MathiasKoch/uwb_localization/Inc/hal.h

/**
  ******************************************************************************
  * @file    hal.h
  * @brief   HAL configuration file.  
  ******************************************************************************
  * @attention
  *
  * <h2><center>&copy; COPYRIGHT(c) 2016 STMicroelectronics</center></h2>
  *
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
  ******************************************************************************
  */ 

/* Define to prevent recursive inclusion -------------------------------------*/
#ifndef __HAL_H
#define __HAL_H

#ifdef __cplusplus
 extern "C" {
#endif

#include "error.h"

#if defined  (STM32F302xC) 
  #include "stm32f3xx_hal.h"
  #include "stm32f3xx.h"

  /* Decawave pin defines */
  #define DECA_SPI_INSTANCE (SPI1)

  #define DECA_CS_PORT (GPIOA)
  #define DECA_CS_PIN (GPIO_PIN_4)

  #define DECA_IRQ_PORT (GPIOB)
  #define DECA_IRQ_PIN (GPIO_PIN_0)
  #define DECA_IRQ_EXTI (EXTI0_IRQn)

  #define DECA_RESET_PORT (GPIOA)
  #define DECA_RESET_PIN (GPIO_PIN_8)

  /* Userbutton pin defines */
  #define USER_BUTTON_PORT (GPIOA)
  #define USER_BUTTON_PIN (GPIO_PIN_1)
  #define USER_BUTTON_EXTI (EXTI1_IRQn)

  /* Enable client SPI (SPI2) */
  #define CLIENT_SPI_INSTANCE (SPI2)

  /* IMU/PRESSURE pin defines */                                                      //------------------ These might still be wrong!
  #define IMU_I2C_INSTANCE (I2C1)

  #define IMU_IRQ_PORT ()
  #define IMU_IRQ_PIN ()
  #define IMU_IRQ_EXTI ()

  /* LED pin defines */                                                      //------------------ These might still be wrong!
  #define LED_1_PORT (GPIOC)
  #define LED_1_PIN (GPIO_PIN_13)
  #define LED_2_PORT (GPIOC)
  #define LED_2_PIN (GPIO_PIN_14)

  /*
  * Everything below here is processor specific defines, and should as such
  * NOT need to be edited! They are specific for the individual processor type,
  * and not implementation specific.
  */

  /* USB pin defines */
  #define USB_PORT (GPIOA)
  #define USBDM_PIN (GPIO_PIN_11)
  #define USBDP_PIN (GPIO_PIN_12)
  #define USB_AF (GPIO_AF14_USB)
  #define USB_EXTI (USB_LP_CAN_RX0_IRQn)

  /* SPI pin defines */
  #define SPI1_PORT (GPIOA)
  #define SPI1_SCK_PIN (GPIO_PIN_5)
  #define SPI1_MISO_PIN (GPIO_PIN_6)
  #define SPI1_MOSI_PIN (GPIO_PIN_7)
  #define SPI1_AF (GPIO_AF5_SPI1)

  #define SPI2_PORT (GPIOB)
  #define SPI2_SCK_PIN (GPIO_PIN_13)
  #define SPI2_MISO_PIN (GPIO_PIN_14)
  #define SPI2_MOSI_PIN (GPIO_PIN_15)
  #define SPI2_AF (GPIO_AF5_SPI2)

  #define DMA1_CHAN2_EXTI (DMA1_Channel2_IRQn)
  #define DMA1_CHAN3_EXTI (DMA1_Channel3_IRQn)

  /* I2C pin defines */
  #define I2C1_PORT (GPIOB)
  #define I2C1_SCL_PIN (GPIO_PIN_6)
  #define I2C1_SDA_PIN (GPIO_PIN_7)
  #define I2C1_AF (GPIO_AF4_I2C1)

  /*
  * The STM32 factory-programmed UUID memory.
  * Three values of 32 bits each starting at this address
  * Use like this: STM32_UUID[0], STM32_UUID[1], STM32_UUID[2]
  */
  #define STM32_UUID ((uint32_t *)0x1FFFF7AC)

  /* DFU Bootloader defines */                                                      //------------------ These might still be wrong!
  #define SYSMEM_RESET_VECTOR (0x1fffC804)
  #define BOOTLOADER_STACK_POINTER (0x20002250)



#elif defined (STM32F10X_MD)
  #include "stm32f1xx_hal.h"
  #include "stm32f1xx.h"


















#elif defined (STM32F072xB)
  #include "stm32f0xx_hal.h"
  #include "stm32f0xx.h"

  /* Decawave pin defines */
  #define DECA_SPI_INSTANCE (SPI1)

  #define DECA_CS_PORT (GPIOA)
  #define DECA_CS_PIN (GPIO_PIN_4)

  #define DECA_IRQ_PORT (GPIOB)
  #define DECA_IRQ_PIN (GPIO_PIN_0)
  #define DECA_IRQ_EXTI (EXTI0_1_IRQn)

  #define DECA_RESET_PORT (GPIOB)
  #define DECA_RESET_PIN (GPIO_PIN_12)

  /* Userbutton pin defines */
  #define USER_BUTTON_PORT (GPIOA)
  #define USER_BUTTON_PIN (GPIO_PIN_1)
  #define USER_BUTTON_EXTI (EXTI0_1_IRQn)

  /* IMU/PRESSURE pin defines */                                                      //------------------ These might still be wrong!
  #define IMU_I2C_INSTANCE (I2C1)

  #define IMU_IRQ_PORT ()
  #define IMU_IRQ_PIN ()
  #define IMU_IRQ_EXTI ()

  /* LED pin defines */                                                      //------------------ These might still be wrong!
  #define LED_1_PORT (GPIOC)
  #define LED_1_PIN (GPIO_PIN_13)
  #define LED_2_PORT (GPIOC)
  #define LED_2_PIN (GPIO_PIN_14)
  #define LED_CHARGING_PORT (GPIOC)
  #define LED_CHARGING_PIN (GPIO_PIN_14)

  /*
  * Everything below here is processor specific defines, and should as such
  * NOT need to be edited! They are specific for the individual processor type,
  * and not implementation specific.
  */

  /* USB pin defines */
  #define USB_AF (GPIO_AF14_USB)
  #define USB_EXTI (USB_IRQn)

  /* SPI pin defines */
  #define SPI1_PORT (GPIOA)
  #define SPI1_SCK_PIN (GPIO_PIN_5)
  #define SPI1_MISO_PIN (GPIO_PIN_6)
  #define SPI1_MOSI_PIN (GPIO_PIN_7)
  #define SPI1_AF (GPIO_AF0_SPI1)

  #define DMA1_CHAN2_3_EXTI (DMA1_Channel2_3_IRQn)

  /* I2C pin defines */
  #define I2C1_PORT (GPIOB)
  #define I2C1_SCL_PIN (GPIO_PIN_6)
  #define I2C1_SDA_PIN (GPIO_PIN_7)
  #define I2C1_AF (GPIO_AF1_I2C1)
  
  /*
  * The STM32 factory-programmed UUID memory.
  * Three values of 32 bits each starting at this address
  * Use like this: STM32_UUID[0], STM32_UUID[1], STM32_UUID[2]
  */
  #define STM32_UUID ((uint32_t *)0x1FFFF7AC)

  /* DFU Bootloader defines */
  #define SYSMEM_RESET_VECTOR (0x1fffC804)
  #define BOOTLOADER_STACK_POINTER (0x20002250)



#else
  #error "Please first define the target STM32Fxxx device used in your application (in a Makefile define)"
#endif

    
#ifdef __cplusplus
}
#endif

#endif /* __HAL_H */

/************************ (C) COPYRIGHT STMicroelectronics *****END OF FILE****/
