MathiasKoch/uwb_localization/Inc/packet.h

/*
 $License:
    Copyright (C) 2010 InvenSense Corporation, All Rights Reserved.
 $
 */
/*******************************************************************************
 * $Id: $
 *******************************************************************************/

/**
 *  @defgroup STM32L STM32L System Layer
 *  @brief  STM32L System Layer APIs.
 *          To interface with any platform, eMPL needs access to various
 *          system layer functions.
 *
 *  @{
 *      @file   packet.h
 *      @brief  Defines needed for sending data/debug packets via USB.
 */

#ifndef __PACKET_H__
#define __PACKET_H__

#ifdef __cplusplus
extern "C" {
#endif


typedef enum {
    PACKET_DATA_ACCEL = 0,
    PACKET_DATA_GYRO,
    PACKET_DATA_COMPASS,
    PACKET_DATA_QUAT,
    PACKET_DATA_EULER,
    PACKET_DATA_ROT,
    PACKET_DATA_HEADING,
    PACKET_DATA_LINEAR_ACCEL,
    NUM_DATA_PACKETS
} eMPL_packet_e;

/**
 *  @brief      Send a quaternion packet via UART.
 *  The host is expected to use the data in this packet to graphically
 *  represent the device orientation. To send quaternion in the same manner
 *  as any other data packet, use eMPL_send_data.
 *  @param[in]  quat    Quaternion data.
 */
void eMPL_send_quat(long *quat);

/**
 *  @brief      Send a DWM packet via UART.
 *  The host is expected to use the data in this packet to graphically
 *  represent the device positions. 
 *  @param[in]  anchorState     Anchor state data.
 *  @param[in]  noAnchors       No of anchors represented in anchorState.
 *  @param[in]  tagState        Tag state data.
 */
void eMPL_send_dwm(float **anchorState, int noAnchors, float *tagState);

/**
 *  @brief      Send a data packet via UART
 *  @param[in]  type    Contents of packet (PACKET_DATA_ACCEL, etc).
 *  @param[in]  data    Data (length dependent on contents).
 */
void eMPL_send_data(unsigned char type, long *data);


#ifdef __cplusplus
}
#endif

#endif /* __PACKET_H__ */

/**
 * @}
 */
