MathiasKoch/uwb_localization/usb_test.ioc

Mcu.UserName=STM32F302CCTx
PA1.Signal=GPIO_Input
PA11.Signal=USB_DM
PA12.Signal=USB_DP
PA13.Signal=SYS_JTMS-SWDIO
PA14.Signal=SYS_JTCK-SWCLK
PA3.Signal=GPXTI3
PA4.Signal=GPIO_Output
PA5.Signal=SPI1_SCK
PA6.Signal=SPI1_MISO
PA7.Signal=SPI1_MOSI
PA8.Signal=GPIO_Input
PA9.Signal=GPXTI9
PB0.Signal=GPXTI0
PB1.Signal=GPIO_Input
PB12.Signal=GPIO_Input
PB13.Signal=SPI2_SCK
PB14.Signal=SPI2_MISO
PB15.Signal=SPI2_MOSI
PB4.Signal=GPXTI4
PB6.Signal=I2C1_SCL
PB7.Signal=I2C1_SDA
PC13.Signal=GPIO_Output
PC14-OSC32_IN.Signal=GPIO_Output
PF0-OSC_IN.Signal=RCC_OSC_IN
PF1-OSC_OUT.Signal=RCC_OSC_OUT
